innovaspace/eduqube/example codes/ground station/upload.h

//-----------------------------------------------------------------------------
//  upload.h
//  Ground Station
//  The upload_data function is declared, so it can be called on main
//-----------------------------------------------------------------------------

#ifndef UPLOAD_H
#define UPLOAD_H

void upload_data();

#endif
