innovaspace/eduqube/example codes/mainboard bme680/radio.h

//-----------------------------------------------------------------------------
//  radio.h
//  Mainboard BME680
//  Functions used in "radio.cpp". Can be called from "main.cpp"
//-----------------------------------------------------------------------------

#ifndef RADIO_H
#define RADIO_H

void radio_setup();
void send_data();

#endif
